tristancollins/HiFi-BabyHuey/LTSpice-EngineersBabyHuey/EngineersBabyHuey.asc

C4: cap; 220n
C5: cap; 220n
D1: LED; RED
D3: LED; RED
M1: nmos; STP8NM60
M2: nmos; STP8NM60
Q1: npn; 2N5551C
Q2: npn; 2N5551C
Q3: npn; 2N5551C
Q4: npn; 2N5551C
Q5: npn; 2N5551C
Q6: npn; 2N5551C
R1: res; 1k
R2: res; 220k
R3: res; 390
R4: res; 47k
R5: res; 220k
R6: res; 1k
R7: res; 470
R9: res; 250
R10: res; 250
R11: res; 680
R12: res; 390
R13: res; 1k
R14: res; 47k
R15: res; 1
R16: res; 1k
R18: res; 1k
R19: res; 220k
R20: res; 10
R21: res; 1k
R22: res; 220k
R23: res; 10
R24: res; 1Meg
R25: res; 47k
R26: res; 22k
R27: res; 1Meg
R39: res; 8
R55: res; 100k
U2: TransPPUL2
U3: tetrode; EL34
U4: tetrode; EL34
U9: triode; 12AX7
U10: triode; 12AX7
V1: voltage; SINE(0 0.27 {Freq}); AC 0.529 0
V3: voltage; 127
V4: voltage; 16.4
V5: voltage; 27.9
VHT: voltage; 400
Named nets: 0, Output, Input, Va, Vbias, Vd-, Vd+
.option noopiter
.options plotwinsize=0
 
;.ac oct 100 10 100k
;.step param R 10k 40k 5k
;.step param R 800 1400 50
;.param T=100-R
 
.INC TubeLib.inc
.INC Cordell-Models.txt
 
.param Freq=1k
.param FFT=16384
.tran 0 {14/Freq} {9/Freq} {14/Freq/FFT}
.four {Freq} V(Output) 5 5
;.tran 0 {11/Freq} {10/Freq} {1/Freq/FFT}
;.four {Freq} I(R39) 5 5
.SUBCKT PrimaryWindings P1 Sg1 B Sg2 P2 Sp1 Sp2
* Push Pull transformer, with Ultralinear taps at 40%
* 6600 to 8 ohms, 3db 1 to 30000 hz
*   
*   
*  model generated by TransformerModels.xls 2022 Apr 06
*  
LP1 1 Sg1 49.2297574999978
LS1 2 B 21.8798922222212
LS2 3 Sg2 21.8798922222212
LP2 4 P2 49.2297574999978
LSA 5 Sp2 0.644556033604859
KALL LP1 LS1 LS2 LP2 LSA 0.999894172238243
RP1 P1 1 82.2
RP2 Sg1 2 54.8
RP3 B 3 54.8
RP4 Sg2 4 82.2
RS Sp1 5 0.1
.ENDS PrimaryWindings
0.27 in gives what looks right out
Engineer's Baby Huey
not the right part but close
